curiouselectric/WindSensor/Wind Sensor PCB/SVG/PCB.png

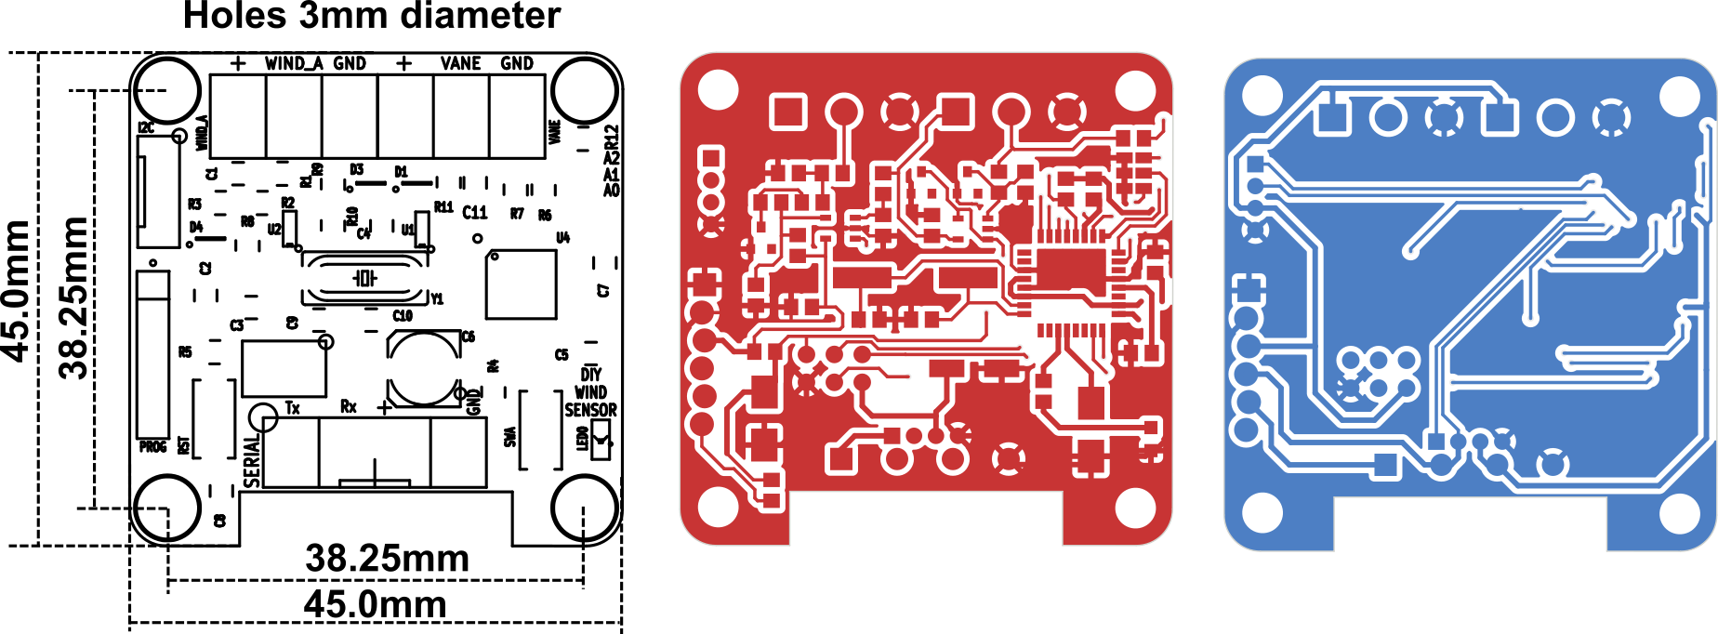
Wind Sensor PCB/SVG/PCB.png
