curiouselectric/WindSensor/Wind Sensor PCB/SVG/Schematic_1.PNG

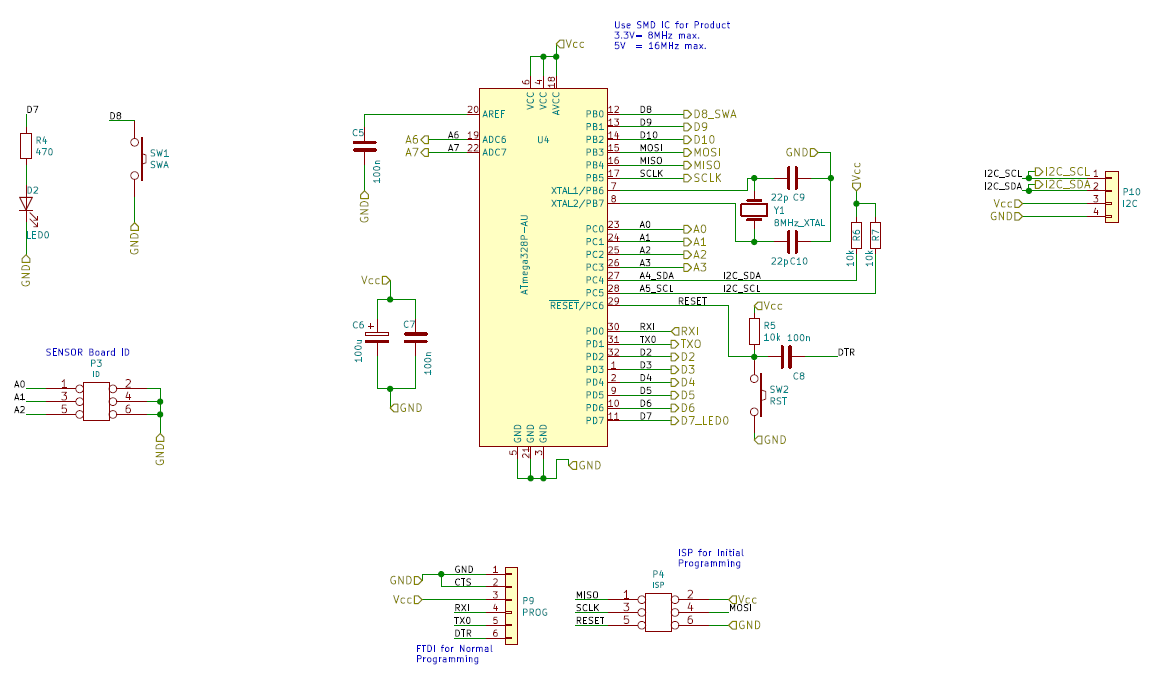
Wind Sensor PCB/SVG/Schematic_1.PNG
