curiouselectric/WindSensor/Wind Sensor PCB/SVG/Schematic_3.PNG.png

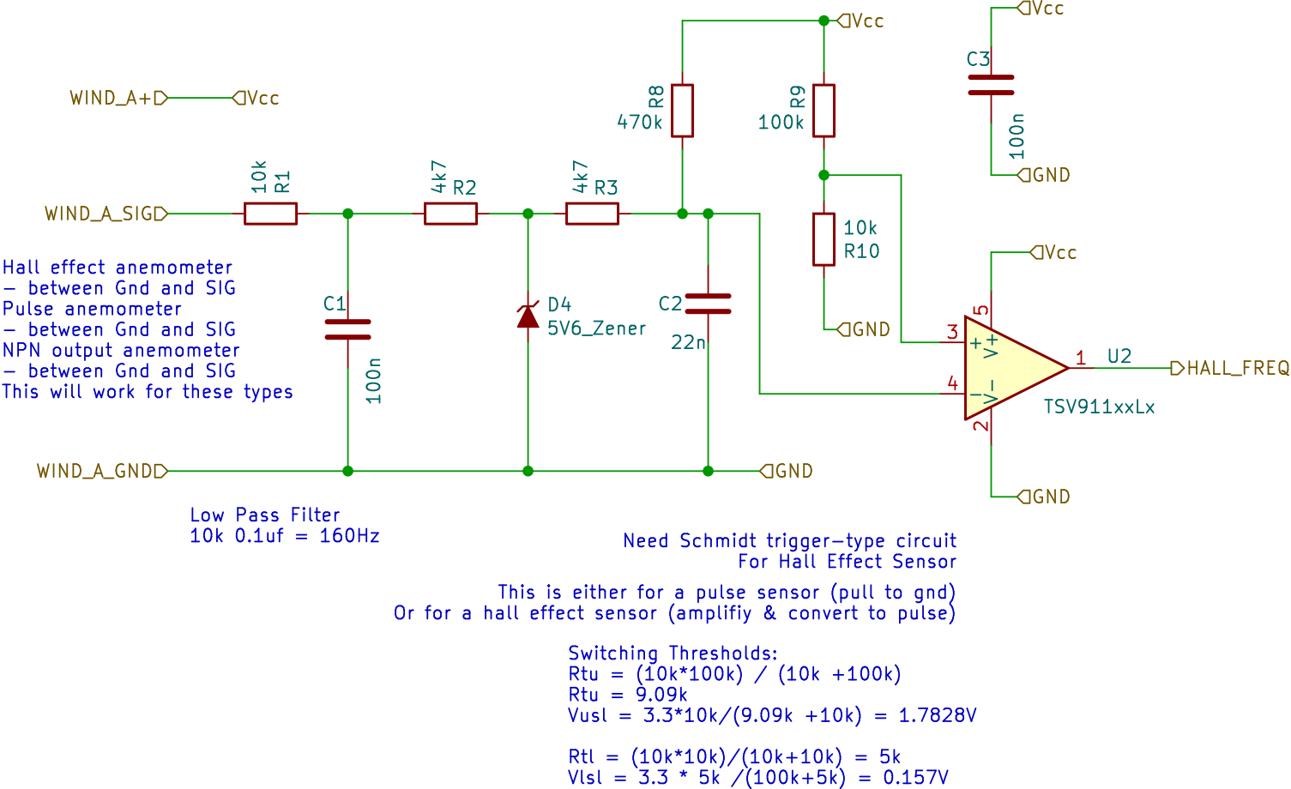
Wind Sensor PCB/SVG/Schematic_3.PNG.png
